satshas/satshakit/media/satshakit_cnc/satshakit_cnc_holes.png

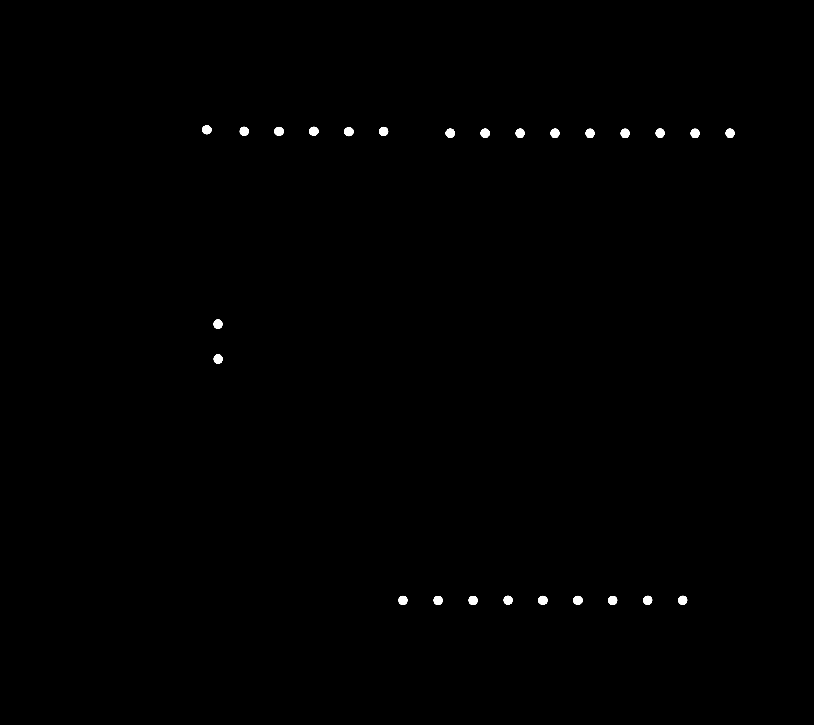
media/satshakit_cnc/satshakit_cnc_holes.png
