satshas/satshakit/media/satshakit_micro/satshakit_micro_holes.png

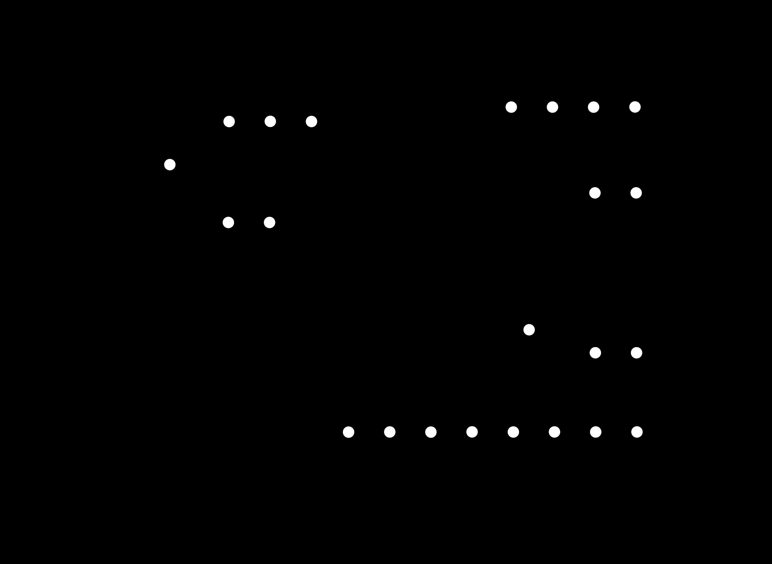
media/satshakit_micro/satshakit_micro_holes.png
