satshas/satshakit/media/satshakit_micro/satshakit_micro_internal.png

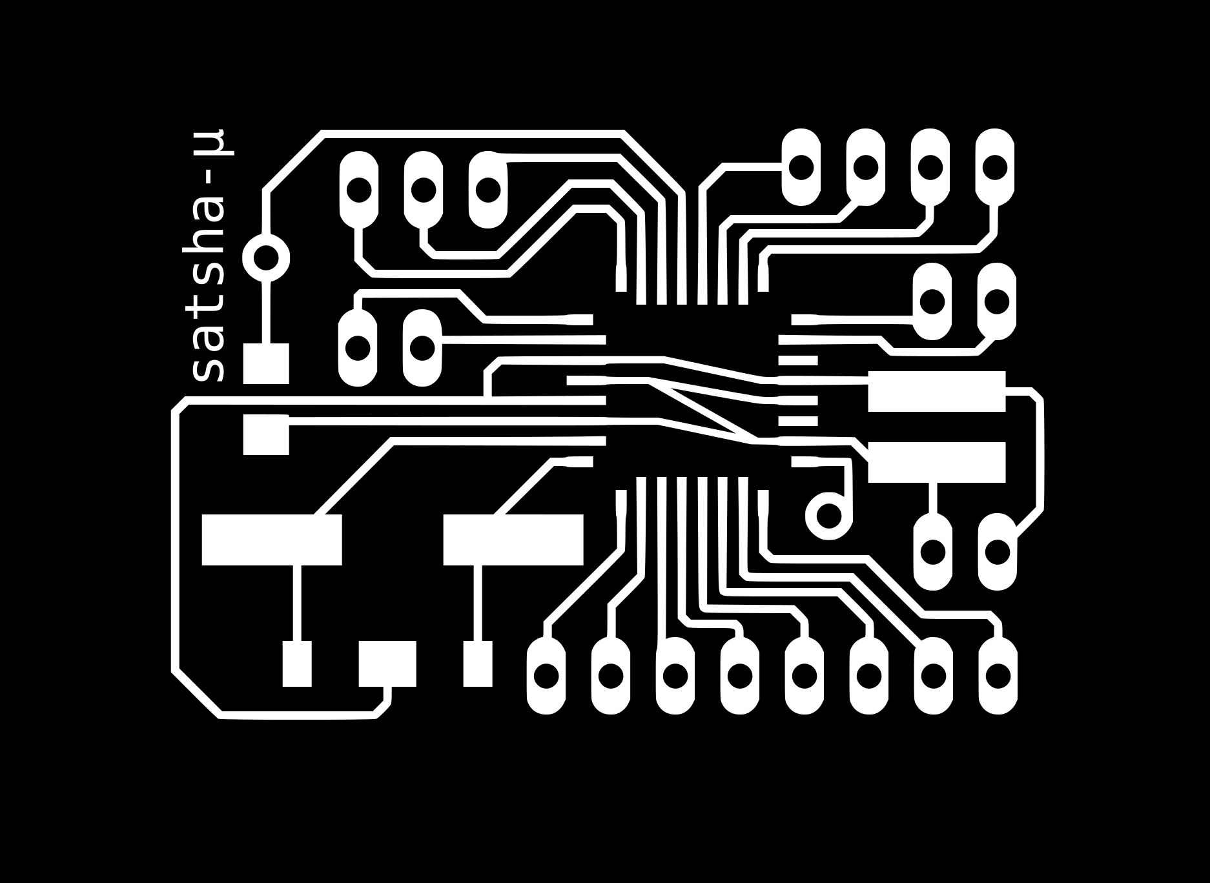
media/satshakit_micro/satshakit_micro_internal.png
